nayman898/van-canbus/hardware/protective-plates/step/pilot_2.50mm/eplzon_38x51_fit_test.step

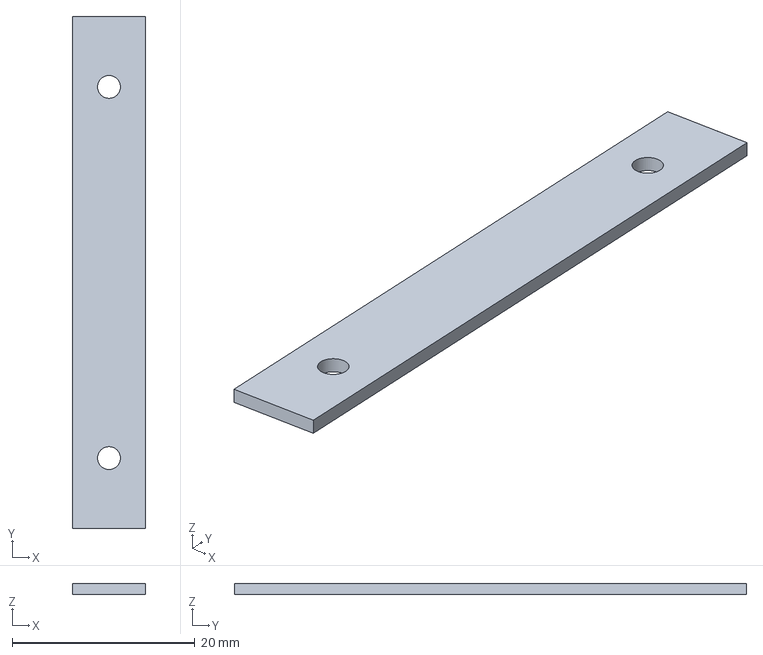
[picture p15: CAD file, 2026-10-06]
hardware/protective-plates/step/pilot_2.50mm/eplzon_38x51_fit_test.step
8.00 x 56.0 x 1.20 mm
