nayman898/van-canbus/hardware/protective-plates/stl/nucleo_drill_to_fit_90x100.stl

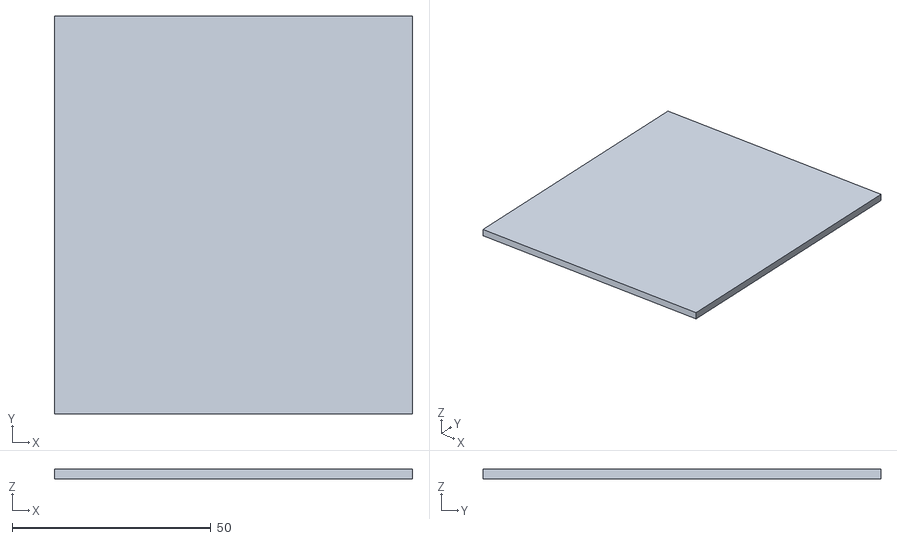
[picture p16: CAD file, 2026-10-06]
hardware/protective-plates/stl/nucleo_drill_to_fit_90x100.stl
90.0 x 100.0 x 2.40
