nayman898/van-canbus/hardware/protective-plates/step/pilot_2.50mm/eplzon_38x51_tray.step

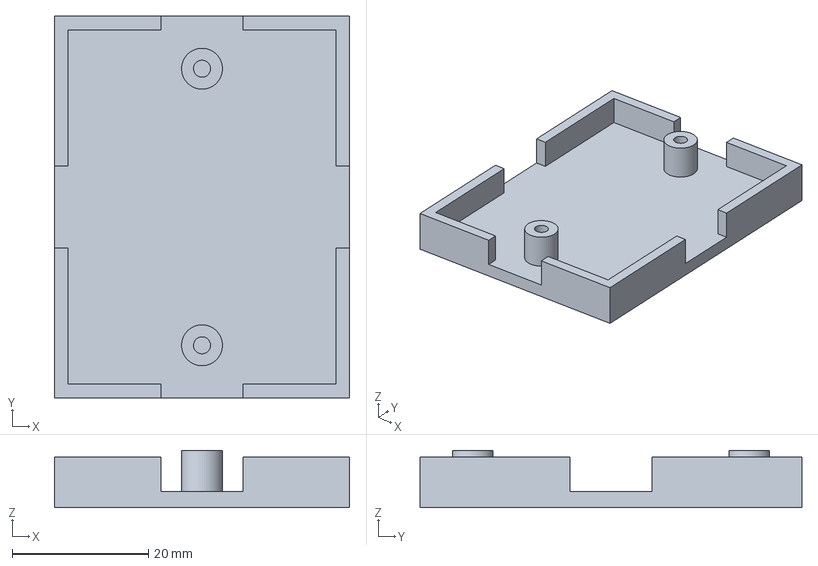
[picture p17: CAD file, 2026-10-06]
hardware/protective-plates/step/pilot_2.50mm/eplzon_38x51_tray.step
43.3 x 56.0 x 8.40 mm
